rolohaun/Defiant/Toolhead/EVA3_Modded.stl

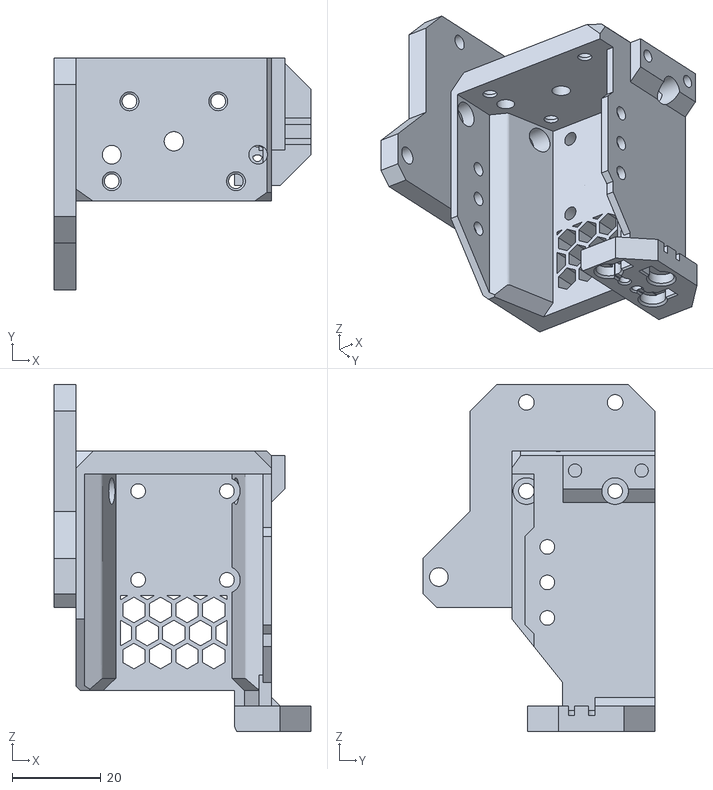
[picture p16: CAD file, 2022-09-19]
Toolhead/EVA3_Modded.stl
57.9 x 52.2 x 78.2
