rolohaun/Defiant/4 X Belt_Clamp.stl

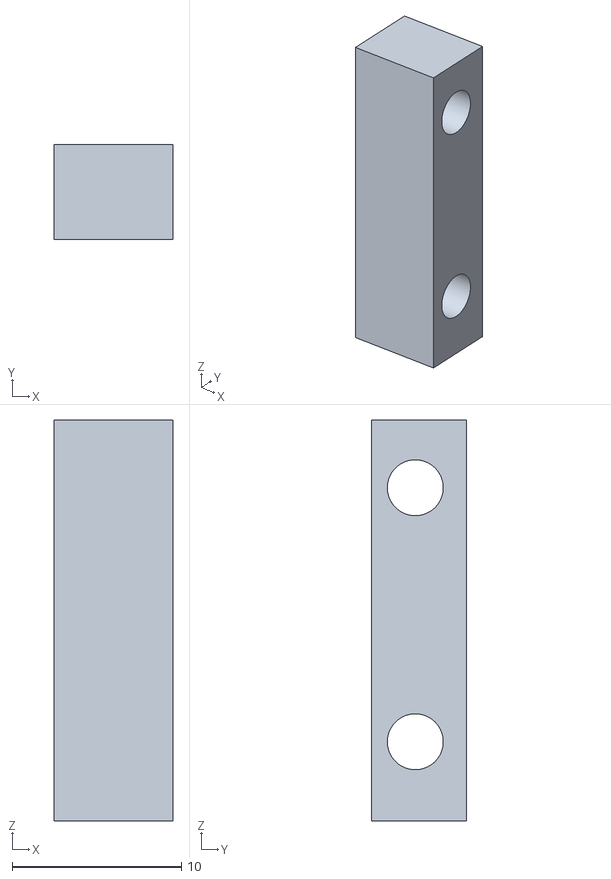
[picture p17: CAD file, 2022-09-19]
4 X Belt_Clamp.stl
7.00 x 5.64 x 23.7
