rolohaun/Defiant/Cooling/Duct_Adapter.stl

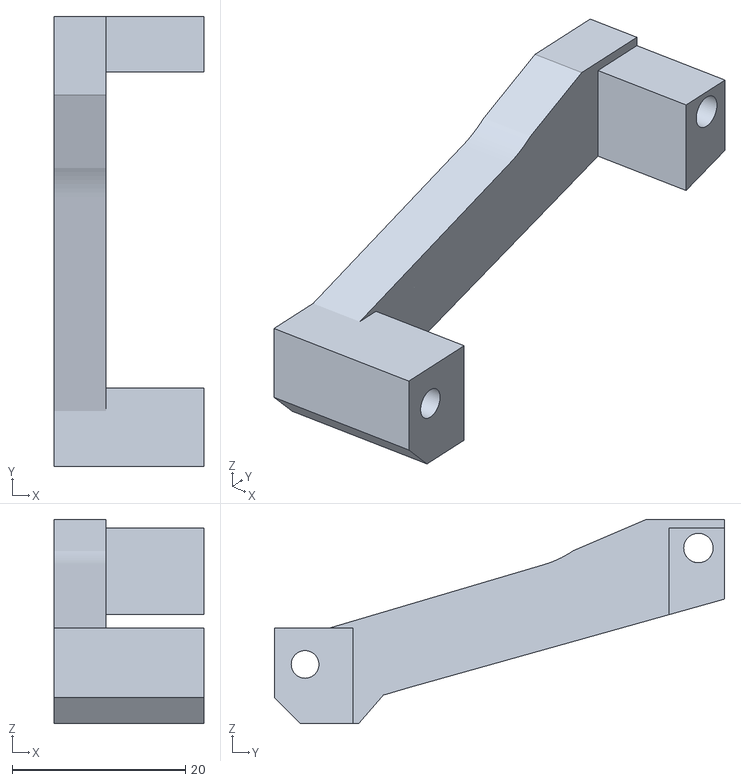
[picture p18: CAD file, 2022-09-19]
Cooling/Duct_Adapter.stl
17.3 x 52.0 x 23.6
