rolohaun/Defiant/Klicky/Klicky_Probe_Dock.stl

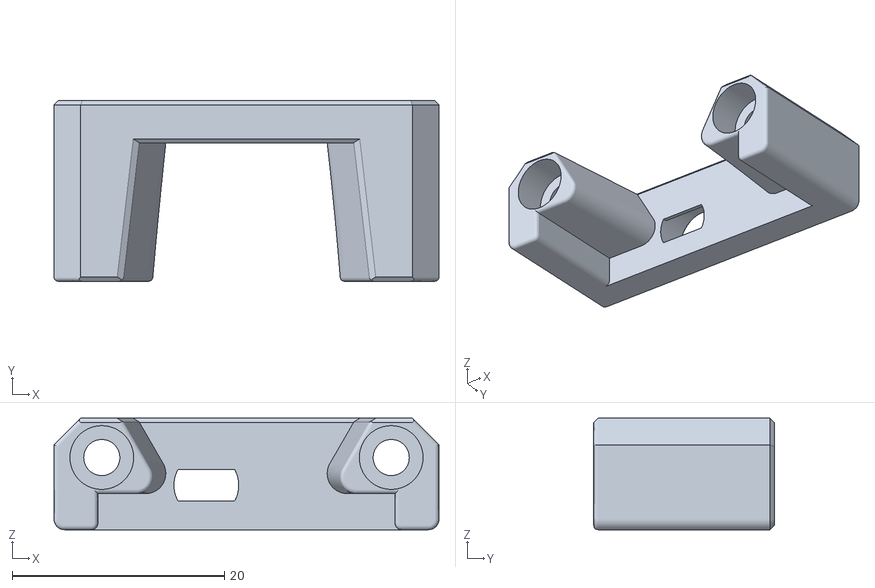
[picture p19: CAD file, 2022-09-19]
Klicky/Klicky_Probe_Dock.stl
36.3 x 17.0 x 10.5
