rolohaun/Defiant/Z Belted Version/1 X Rear_Belted_Z_Bed_Mount.stl

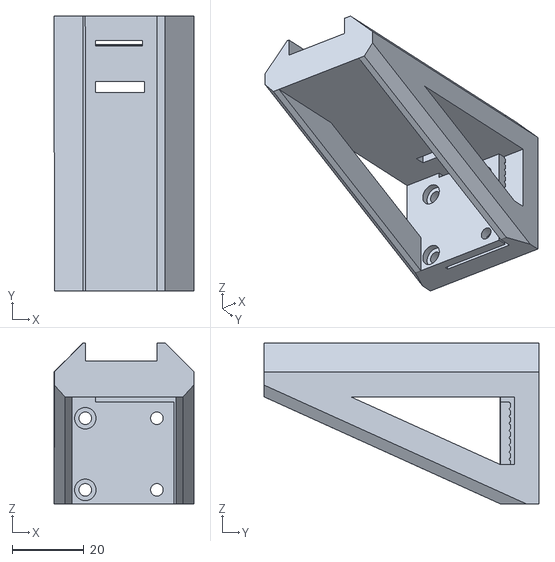
[picture p20: CAD file, 2022-09-19]
Z Belted Version/1 X Rear_Belted_Z_Bed_Mount.stl
39.0 x 76.8 x 44.9
