rolohaun/Defiant/Rear_Touch_Plate.stl

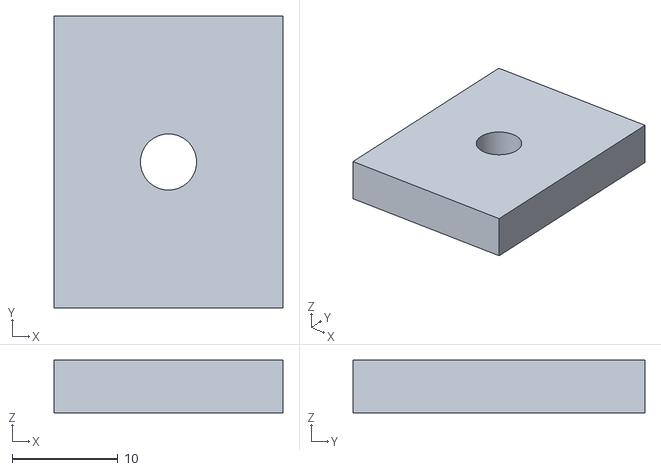
[picture p21: CAD file, 2022-09-19]
Rear_Touch_Plate.stl
21.6 x 27.6 x 5.00
