rolohaun/Defiant/Z Belted Version/1 X Rear_Belted_Z_Motor_Mount.stl

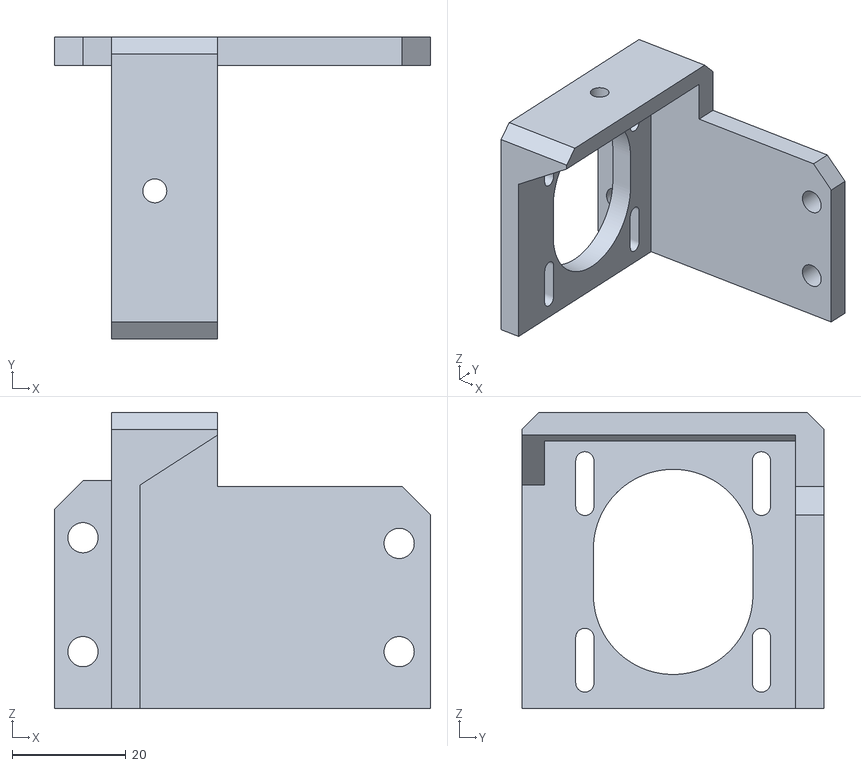
[picture p22: CAD file, 2022-09-19]
Z Belted Version/1 X Rear_Belted_Z_Motor_Mount.stl
66.0 x 53.1 x 52.0
