rolohaun/Defiant/4 X Belt_Slide.stl

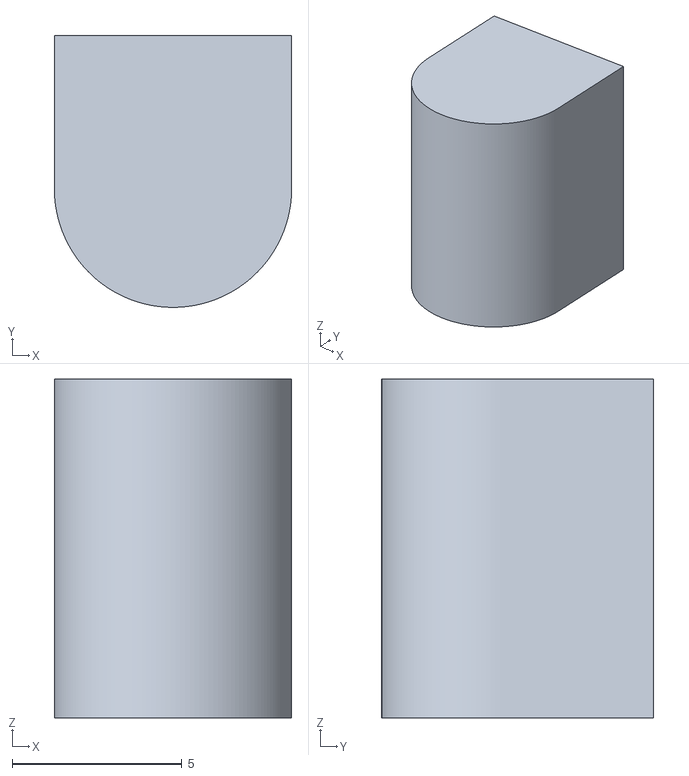
[picture p23: CAD file, 2022-09-19]
4 X Belt_Slide.stl
7.00 x 8.01 x 10.0
