rolohaun/Defiant/Z Belted Version/1 X Right_Belted_Z_Idler_Mount.stl

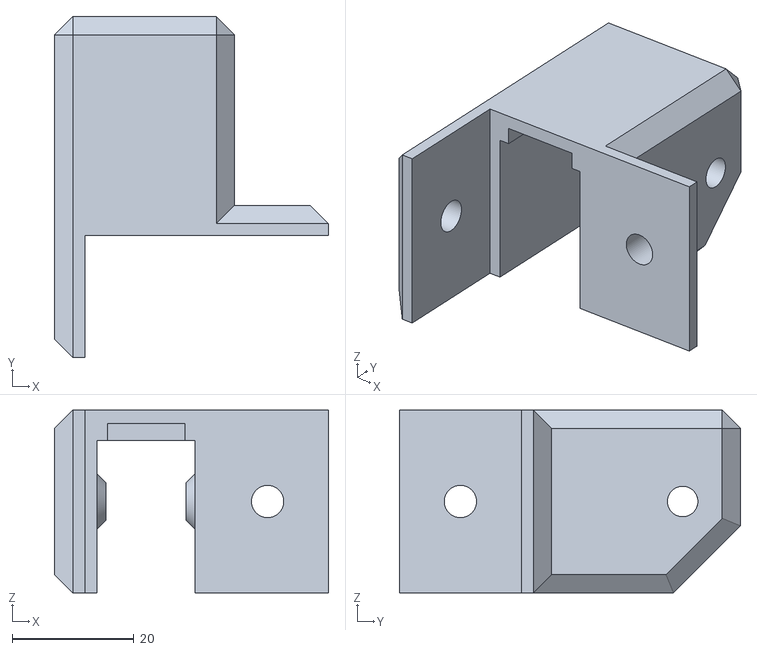
[picture p24: CAD file, 2022-09-19]
Z Belted Version/1 X Right_Belted_Z_Idler_Mount.stl
45.0 x 56.0 x 30.0
