rolohaun/Defiant/Z Belted Version/1 X Left_Belted_Z_Motor_Mount.stl

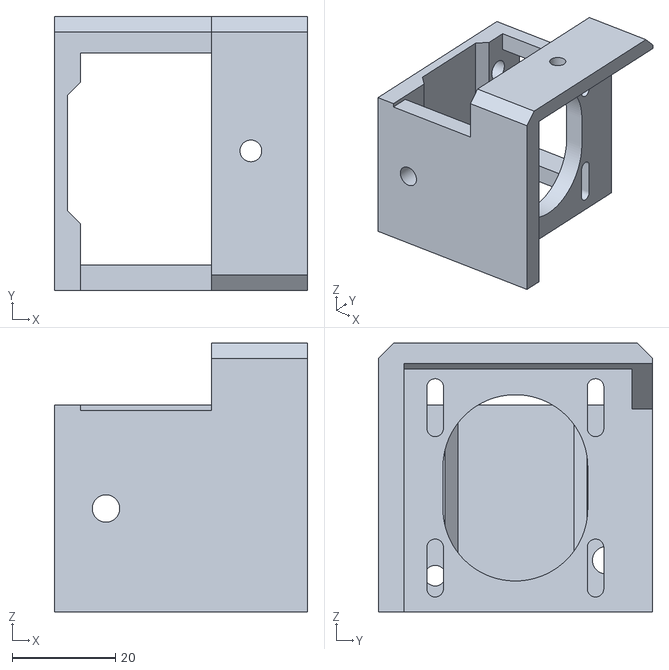
[picture p25: CAD file, 2022-09-19]
Z Belted Version/1 X Left_Belted_Z_Motor_Mount.stl
49.0 x 53.1 x 52.0
