rolohaun/Defiant/Z Belted Version/1 X Rear_Belted_Z_Idler_Mount.stl

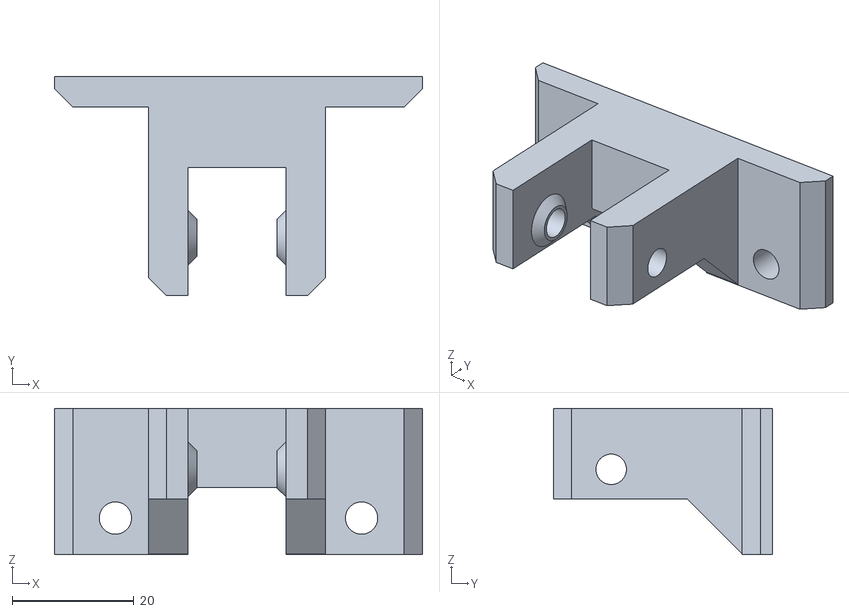
[picture p26: CAD file, 2022-09-19]
Z Belted Version/1 X Rear_Belted_Z_Idler_Mount.stl
60.4 x 36.0 x 24.0
